waterloo-rocketry/ST_PATS/src/display.h

#pragma once
#include <Adafruit_SharpMem.h>

static constexpr int DISPLAY_W = 400;
static constexpr int DISPLAY_H = 240;
static constexpr int LINE_H = 18;
static constexpr int LED = 13;

extern Adafruit_SharpMem display;
